bogdanbacila/apl-microphone-turntable/photos/IMG_20200703_163600.jpg

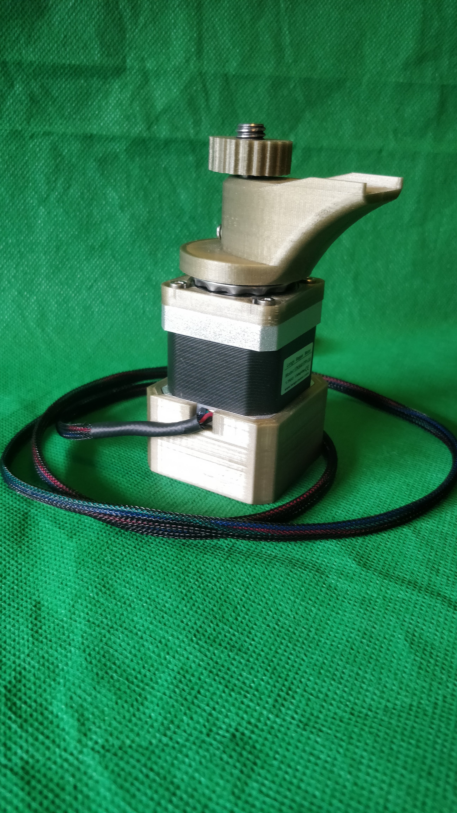
photos/IMG_20200703_163600.jpg
