bogdanbacila/apl-microphone-turntable/photos/IMG_20200703_163646.jpg

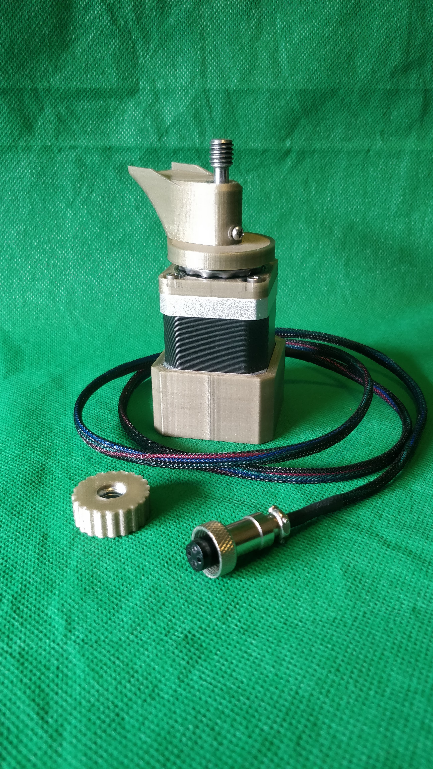
photos/IMG_20200703_163646.jpg
