bogdanbacila/apl-microphone-turntable/photos/IMG_20200703_163923.jpg

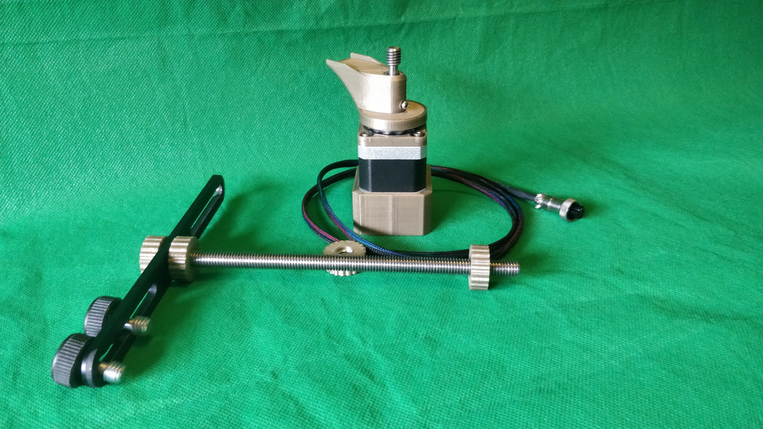
photos/IMG_20200703_163923.jpg
