bogdanbacila/apl-microphone-turntable/photos/IMG_20200703_164057.jpg

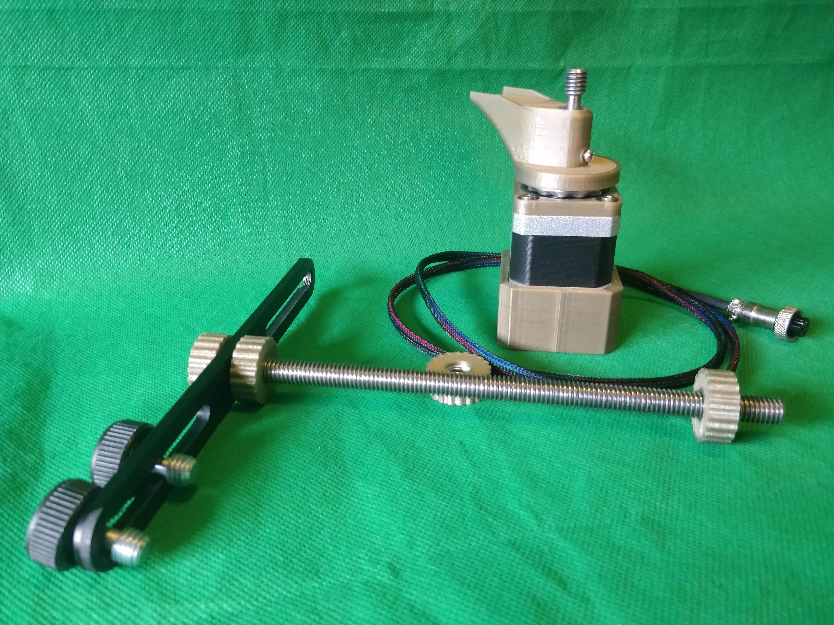
photos/IMG_20200703_164057.jpg
