bogdanbacila/apl-microphone-turntable/photos/IMG_20200703_164115.jpg

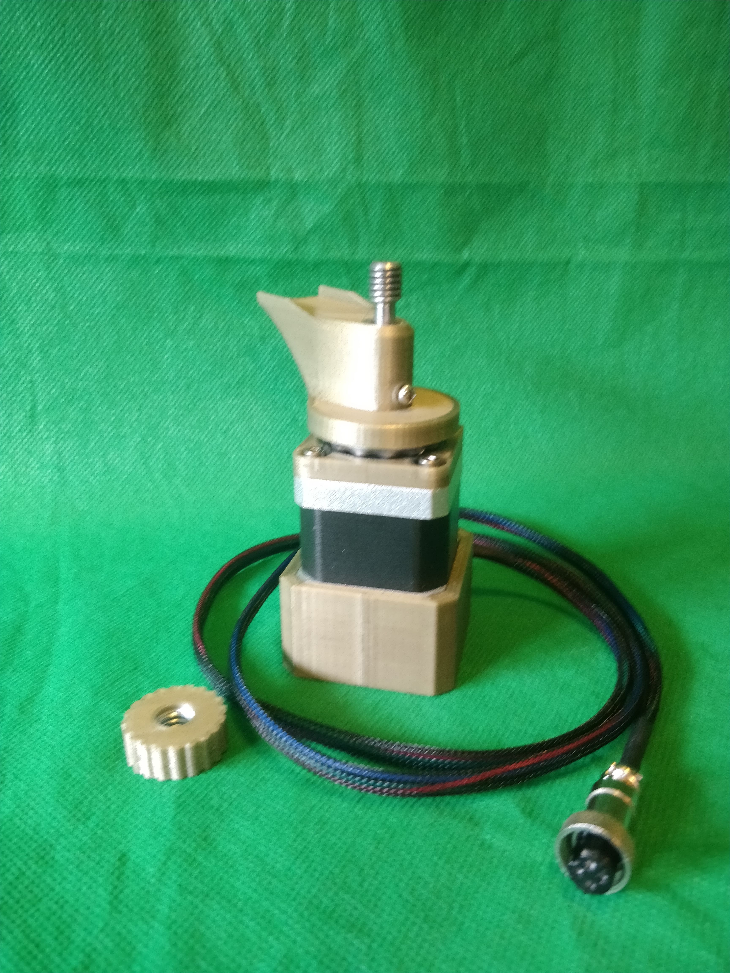
photos/IMG_20200703_164115.jpg
