bogdanbacila/apl-microphone-turntable/photos/IMG_20200703_164141.jpg

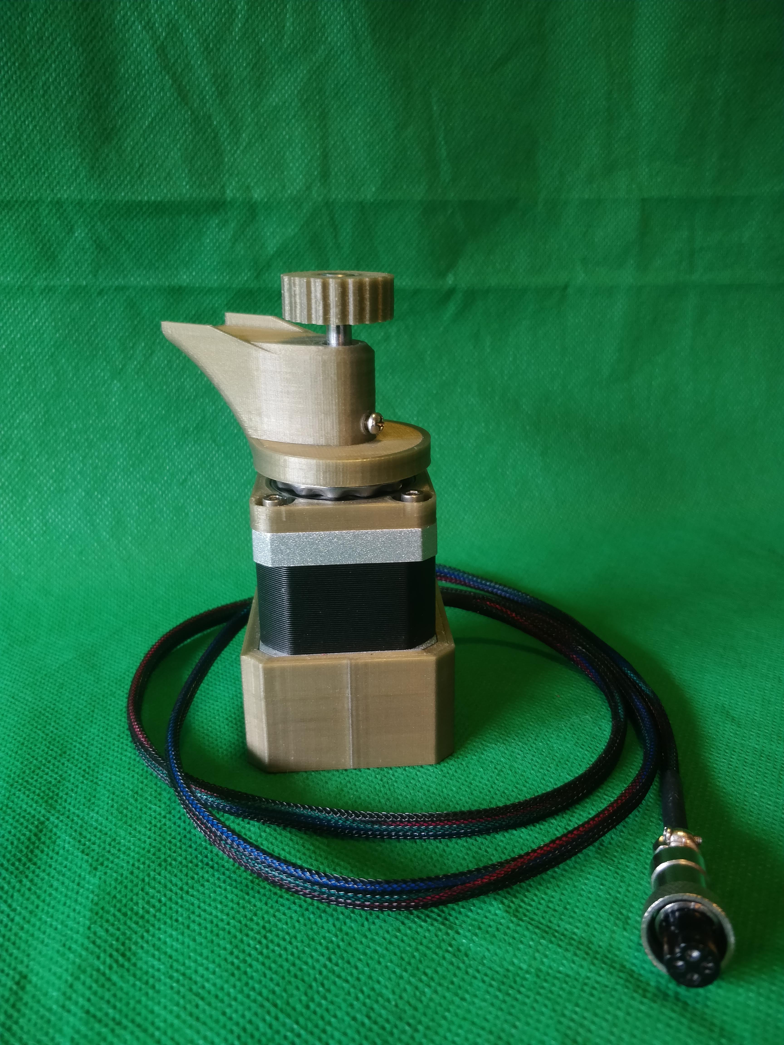
photos/IMG_20200703_164141.jpg
