bogdanbacila/apl-microphone-turntable/photos/IMG_20200703_164520.jpg

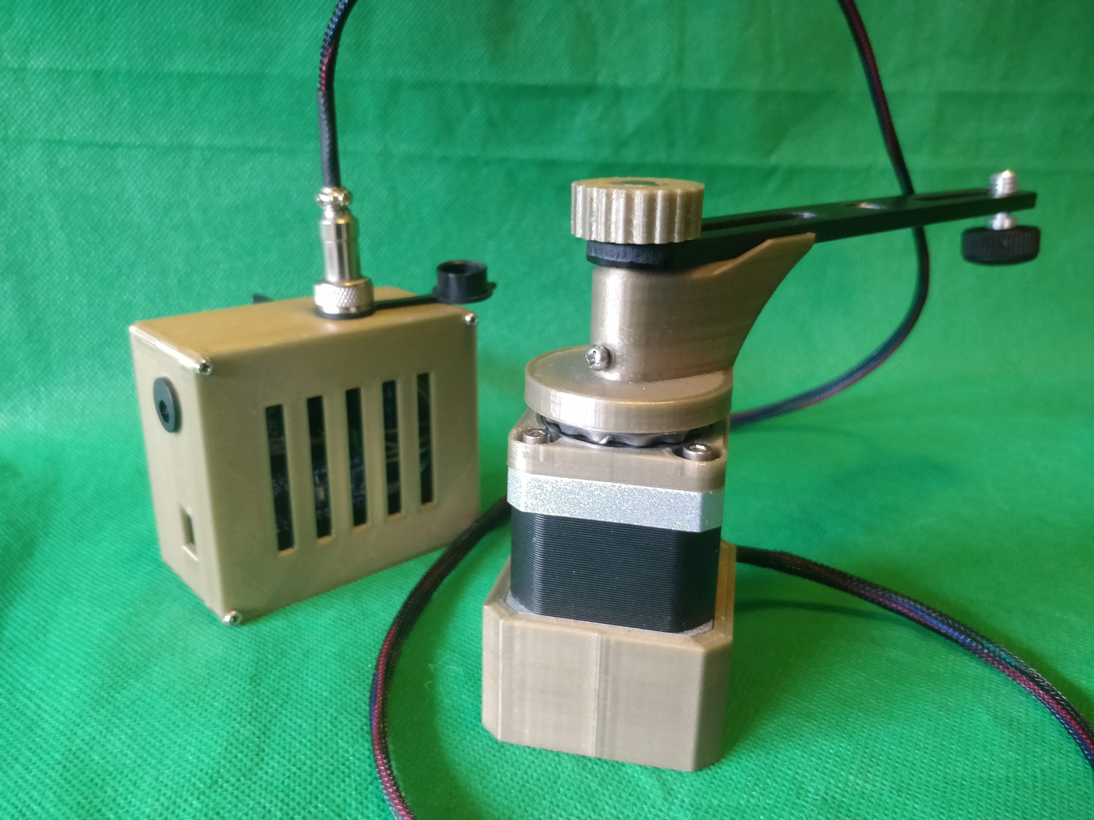
photos/IMG_20200703_164520.jpg
