bogdanbacila/apl-microphone-turntable/photos/IMG_20200703_164552.jpg

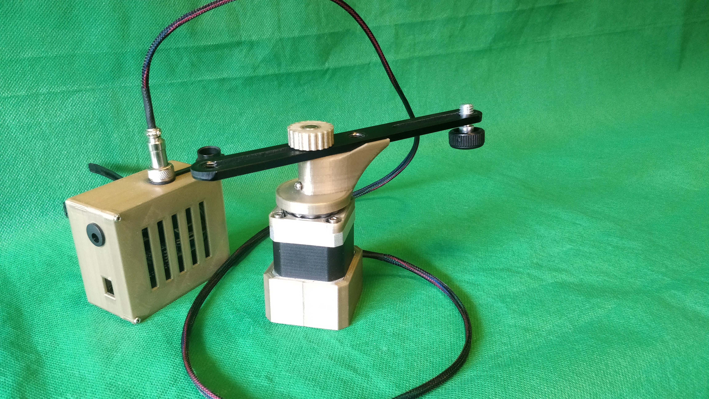
photos/IMG_20200703_164552.jpg
