bogdanbacila/apl-microphone-turntable/photos/IMG_20200703_164702.jpg

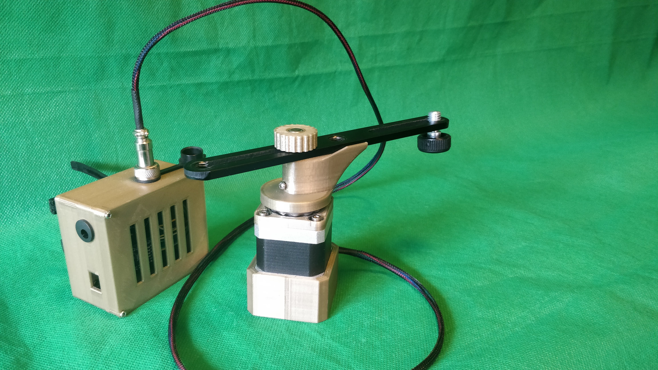
photos/IMG_20200703_164702.jpg
