bogdanbacila/apl-microphone-turntable/photos/IMG_20200703_164803.jpg

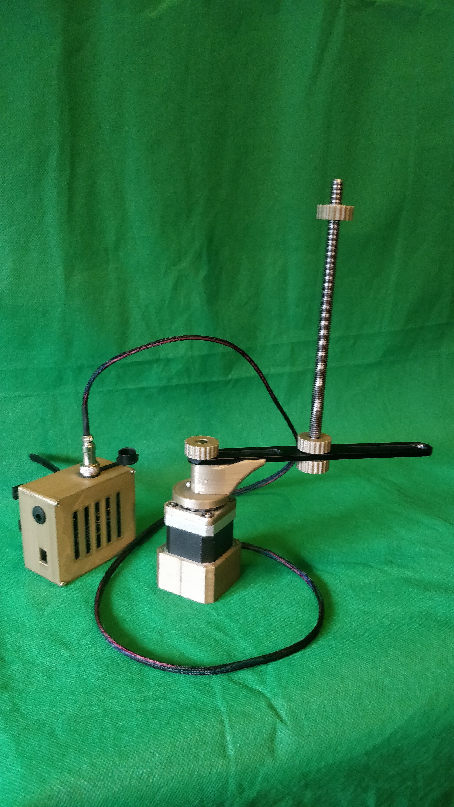
photos/IMG_20200703_164803.jpg
