bogdanbacila/apl-microphone-turntable/photos/IMG_20200703_164817.jpg

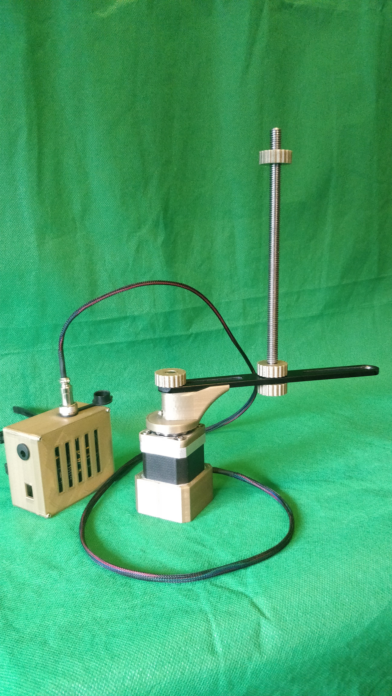
photos/IMG_20200703_164817.jpg
