bogdanbacila/apl-microphone-turntable/photos/IMG_20200703_164829.jpg

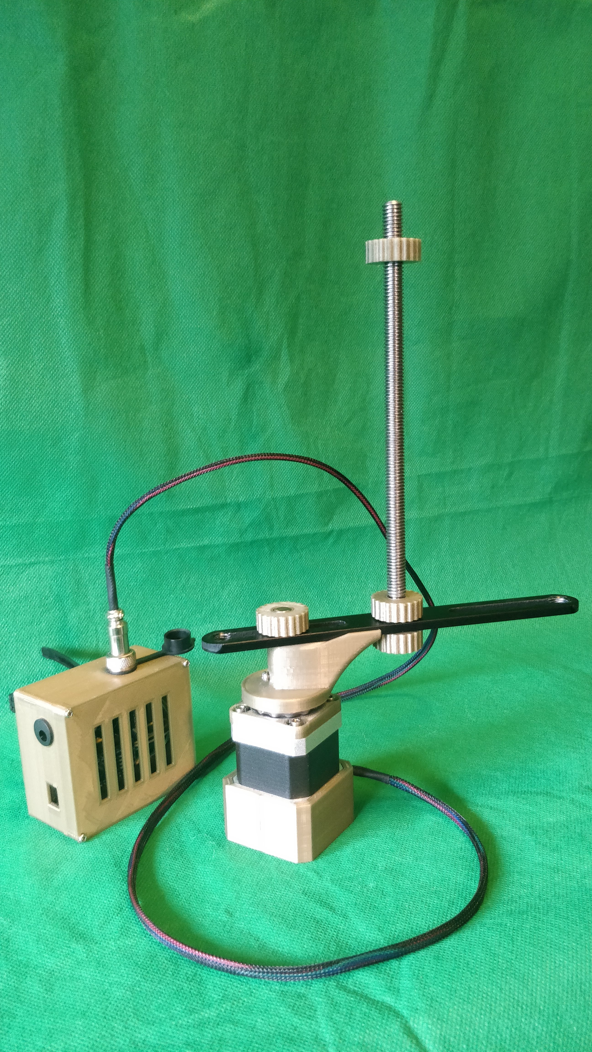
photos/IMG_20200703_164829.jpg
