bogdanbacila/apl-microphone-turntable/photos/IMG_20200703_165136.jpg

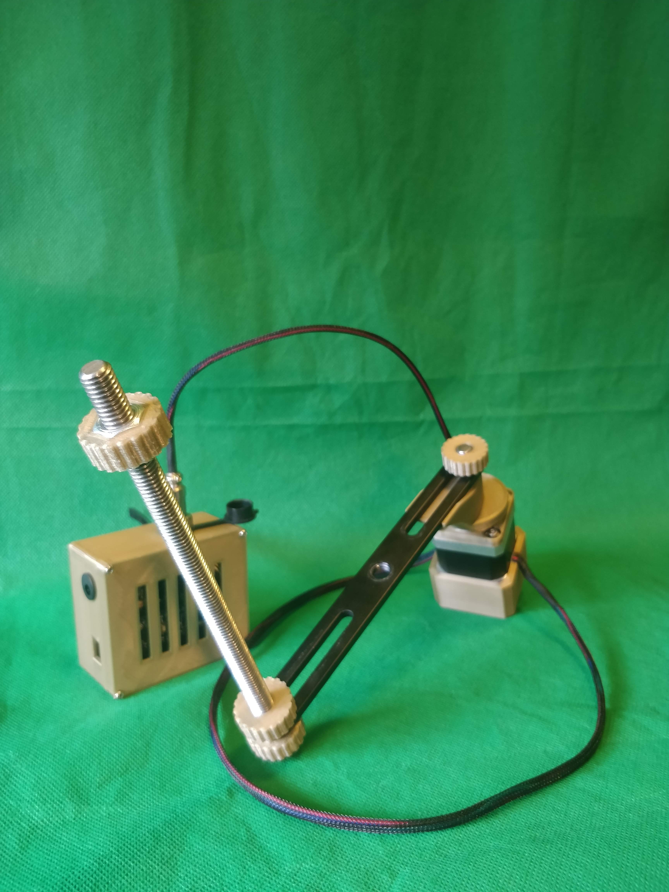
photos/IMG_20200703_165136.jpg
