bogdanbacila/apl-microphone-turntable/photos/IMG_20200703_165221.jpg

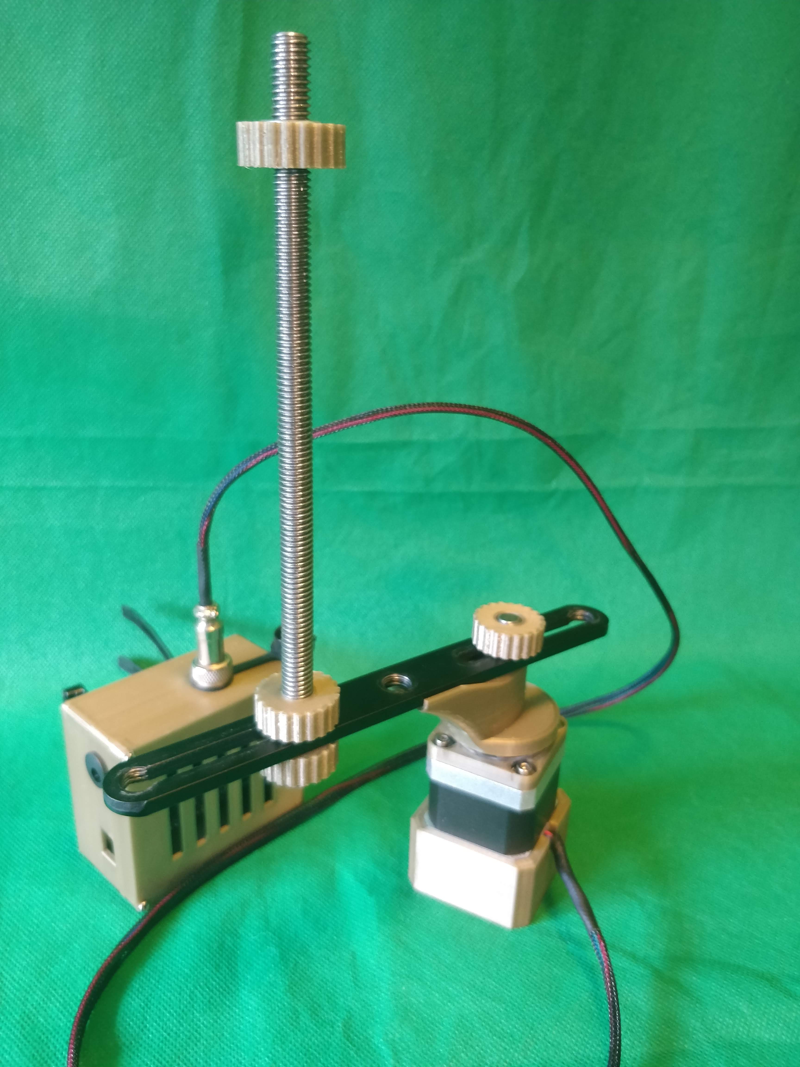
photos/IMG_20200703_165221.jpg
