bogdanbacila/apl-microphone-turntable/photos/IMG_20200703_165330.jpg

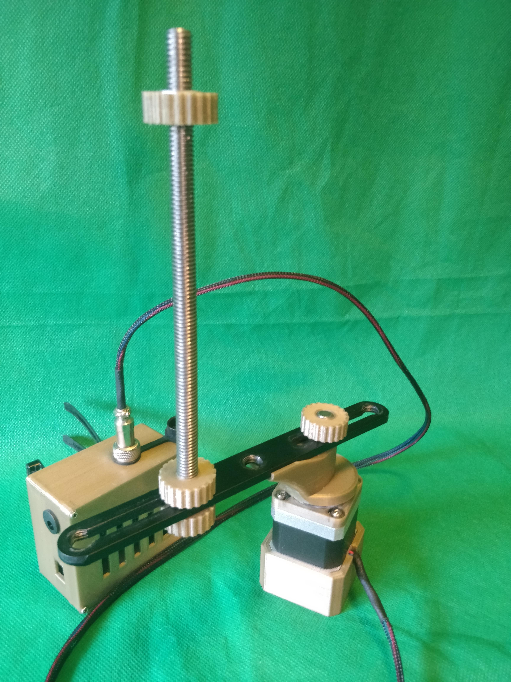
photos/IMG_20200703_165330.jpg
