bogdanbacila/apl-microphone-turntable/photos/IMG_20200703_165343.jpg

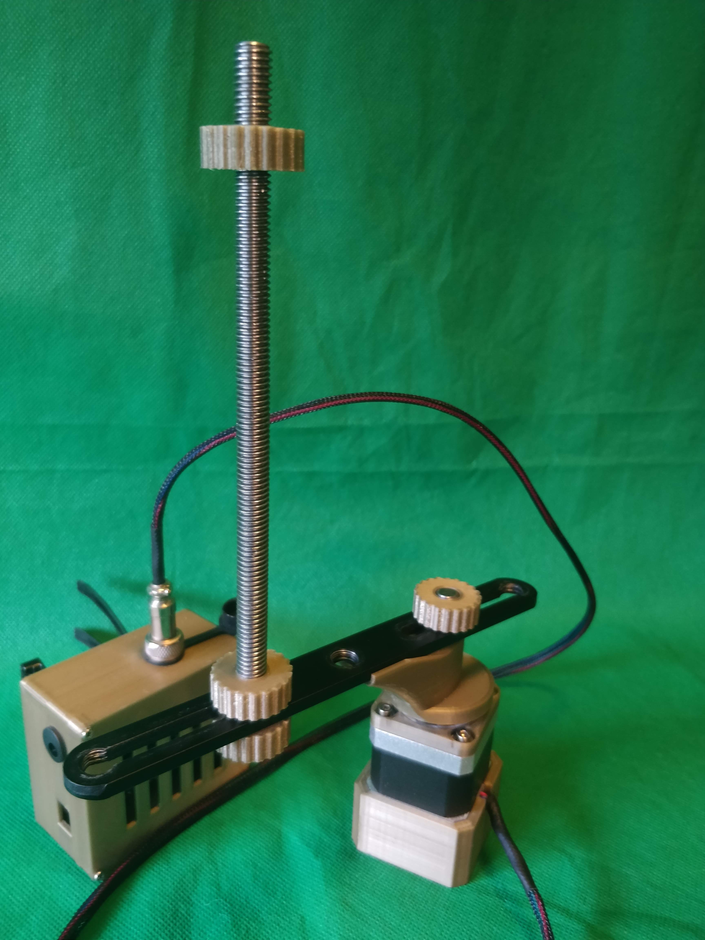
photos/IMG_20200703_165343.jpg
