bogdanbacila/apl-microphone-turntable/photos/IMG_20200703_165440.jpg

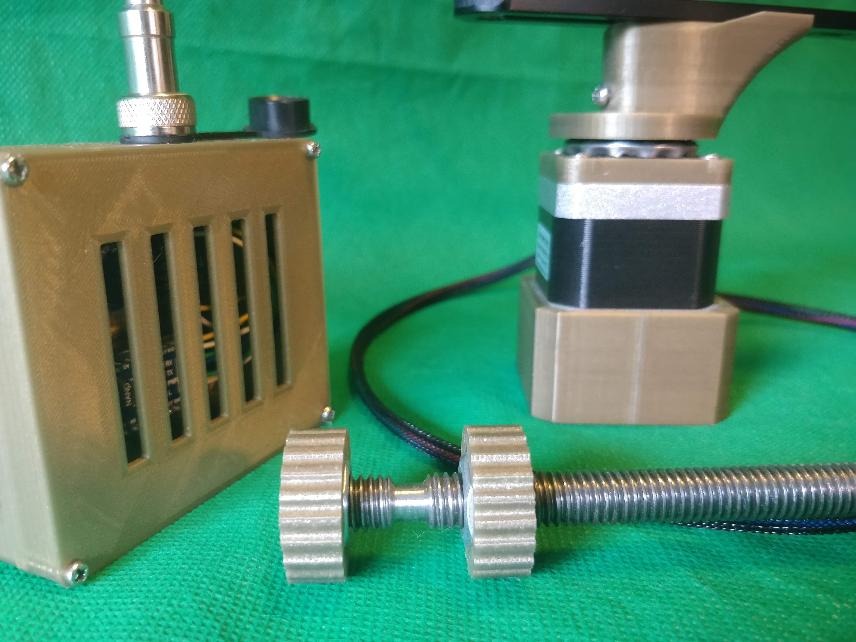
photos/IMG_20200703_165440.jpg
