bogdanbacila/apl-microphone-turntable/photos/IMG_20200703_165643.jpg

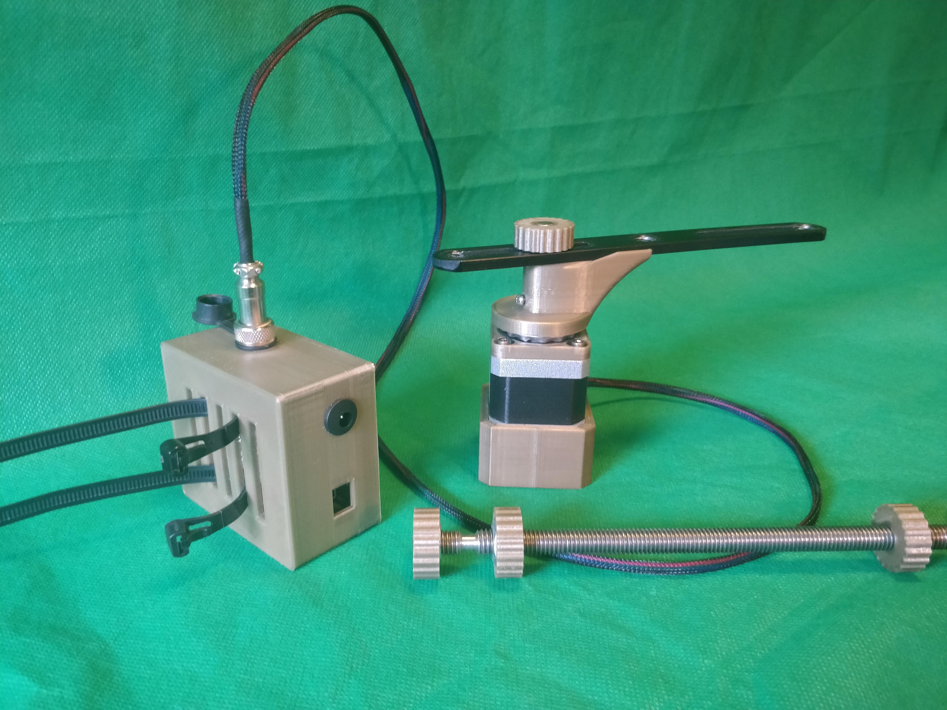
photos/IMG_20200703_165643.jpg
