bogdanbacila/apl-microphone-turntable/photos/IMG_20200703_165652.jpg

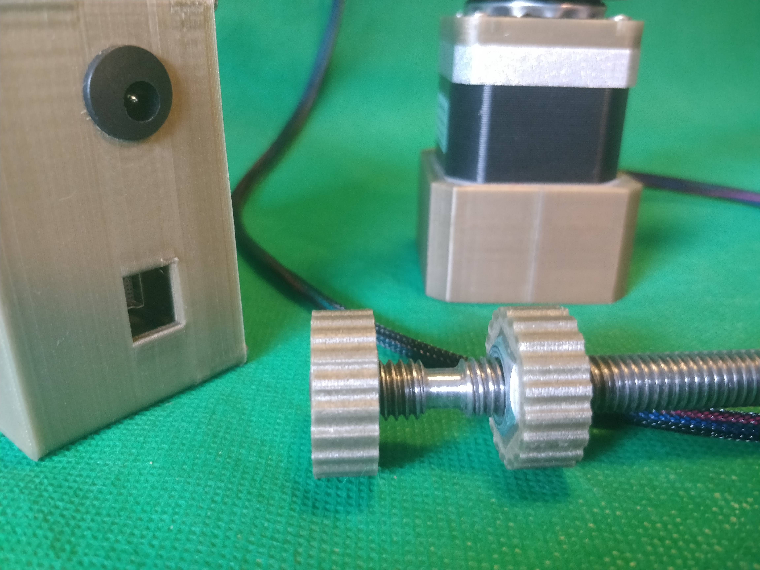
photos/IMG_20200703_165652.jpg
