bogdanbacila/apl-microphone-turntable/screenshots/Screenshot 2020-07-03 at 17.51.06.png

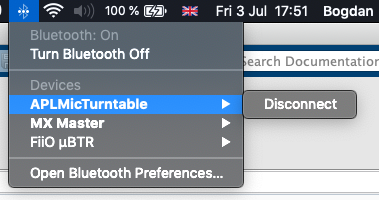
screenshots/Screenshot 2020-07-03 at 17.51.06.png
