bogdanbacila/apl-microphone-turntable/screenshots/Screenshot 2020-07-03 at 17.52.04.png

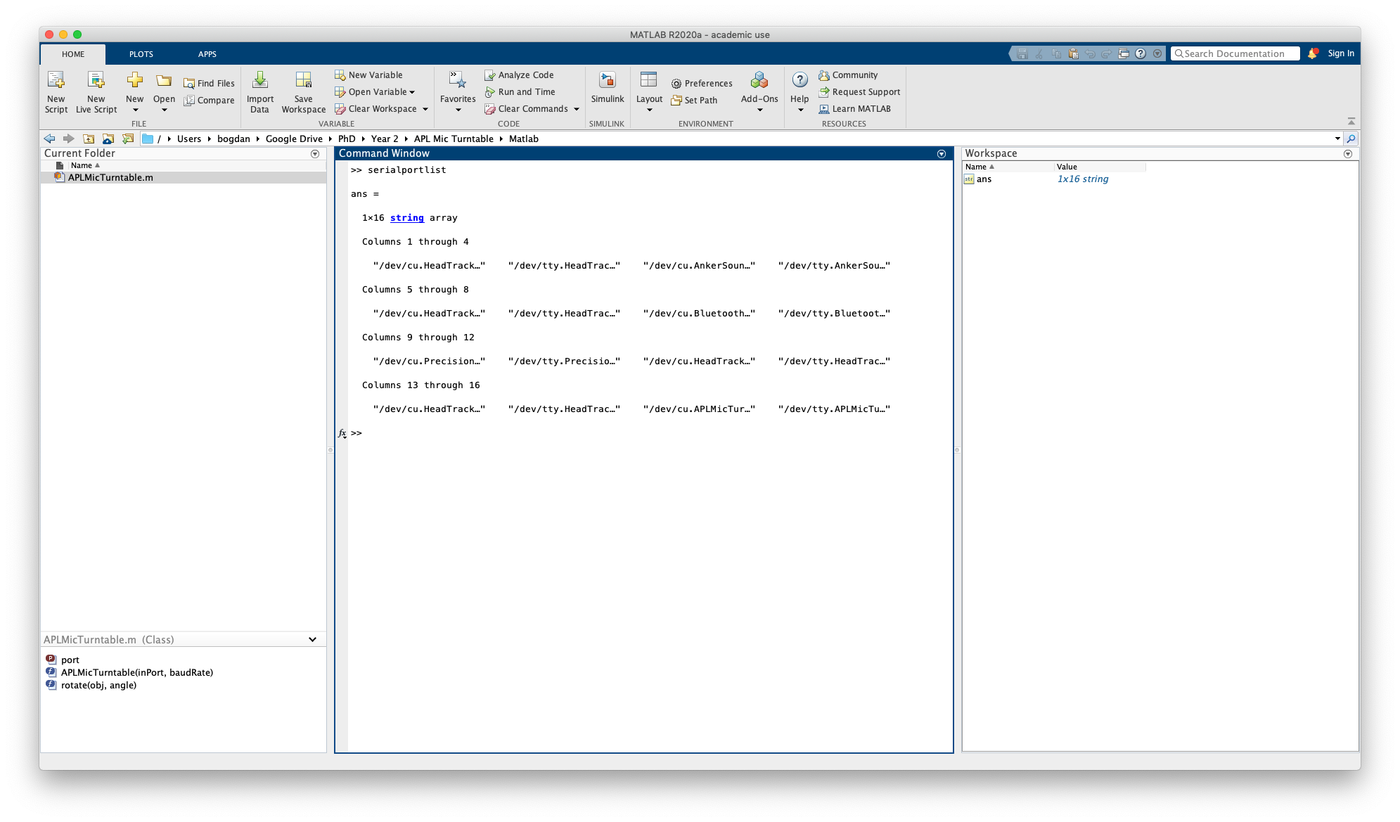
screenshots/Screenshot 2020-07-03 at 17.52.04.png
